Ma-Lab-Cal/Lab-Digital-Twin/firmware/tests/MMC5983MA_test/MMC5983MA_test.ino

/**
 * @file example_1_read_data.ino
 * @date 2022-03-08
 *
 * @copyright Copyright (c) 2022
 *
 * Read magnetic field data from MMC5983MA.
 *
 */

#include "rath_MMC5983MA.h"

rath::MMC5983MA sensor = rath::MMC5983MA();  // I2C address for PMSA003I is 0x12

void setup() {
  Serial.begin(115200);

  sensor.init();

  Serial.println("ready.");

  Serial.print("Sensor ID: "); Serial.println(sensor.getID());
}

void loop() {
  rath::MMC5983MA::DataFrame data_frame = sensor.get();
  float x = data_frame.x;
  float y = data_frame.y;
  float z = data_frame.z;
  
  float temperature = sensor.getTemperature();

  Serial.print("x: ");  Serial.print(x);  Serial.print(" mT\t");
  Serial.print("y: ");  Serial.print(y);  Serial.print(" mT\t");
  Serial.print("z: ");  Serial.print(z);  Serial.print(" mT\t");
  Serial.print("temperature: ");  Serial.print(temperature);  Serial.print(" C");
  Serial.println();

  delay(100);
}
